Protoser/buttonbox/src/settings.h

// Persistent user settings (NVS flash).
#pragma once
#include <Arduino.h>

static const uint8_t APP_ORDER_MAX = 13;  // launcher-order capacity (>= number of apps in ui.cpp APPS)
static const uint8_t MCDU_MAP_N    = 14;  // physical buttons remappable on the MCDU page (== NUM_HID)
static const uint8_t KEYMAP_N      = 32;  // keyboard binding per output: 0..13 physical, 14..31 chord outputs

// Keyboard modifier bits (settings.keyMod entries) — match the HID left-modifier byte.
static const uint8_t KM_CTRL  = 0x01;
static const uint8_t KM_SHIFT = 0x02;
static const uint8_t KM_ALT   = 0x04;
static const uint8_t KM_GUI   = 0x08;

// Flight-display unit flags (settings.flightUnits bitfield).
static const uint8_t FU_SPEED_MPH = 0x01;  // airspeed in mph (else kt)
static const uint8_t FU_ALT_M     = 0x02;  // altitude in metres (else ft)

// Clock app display flags (settings.clockFlags bitfield).
static const uint8_t CLK_DIGITAL  = 0x01;  // digital readout (else analog dial)
static const uint8_t CLK_SECONDS  = 0x02;  // show the seconds hand / digital seconds
static const uint8_t CLK_NUMERALS = 0x04;  // analog: draw 12/3/6/9 numerals
static const uint8_t CLK_DATE     = 0x08;  // show the weekday/date line
static const uint8_t CLK_24H      = 0x10;  // digital: 24-hour (else 12-hour AM/PM)

struct Settings {
  bool     flipped       = false;  // when true: no screen rotation (panel in non-default position)
  bool     labelsGpio    = false;  // grid labels: false = HID number, true = GPIO
  uint16_t idleBlankSec  = 0;      // blank screen after N s idle (0 = never)
  uint16_t chordWindowMs = 40;     // hold window before a chord member fires solo
  uint8_t  bootSel        = 1;      // power-on screen: 0 = launcher, else app index+1 (see ui.cpp APPS)
  uint8_t  pcStatOrder[5] = {0, 1, 2, 3, 4};  // ordered stat indices 0-7 shown on dash; 0xFF = empty slot
  uint8_t  appOrder[APP_ORDER_MAX] = {0, 1, 2, 3, 4, 5, 6, 7, 8};  // launcher order; values index ui.cpp APPS
  uint16_t appHidden      = 0;               // bitmask: bit i set = app i hidden from launcher (Menu never hidden)
  uint8_t  wifiMode       = 2;               // 0=off, 1=always on, 2=auto (via companion when connected)
  // MCDU page: physical button (HID index) -> MCDU output index (see mcdu.cpp MCDU_OUTPUTS).
  // Default: 5x2 grid -> LSK L1/R1..L5/R5, nav -> scroll + OVFY/CLR.
  uint8_t  mcduMap[MCDU_MAP_N] = {3, 9, 4, 10, 5, 11, 6, 12, 7, 13, 1, 2, 17, 16};
  uint8_t  flightUnits    = 0;               // FU_* bitfield (speed/altitude units on the Flight display)
  uint8_t  engStyle       = 0;               // Engine view: 0 = dial gauges, 1 = bars
  uint16_t timerSec       = 300;             // countdown Timer app: last-used duration (s)
  // Keyboard output: per-output HID key + modifier. Output index (0..13 physical, 14..31 chord).
  // keyKey 0 = unbound (that output emits nothing). Default: the 10 always-on buttons -> F13..F22
  // (phantom keys no real keyboard has, so they never collide); nav + chords start unbound.
  uint8_t  keyKey[KEYMAP_N] = {0x68, 0x69, 0x6A, 0x6B, 0x6C, 0x6D, 0x6E, 0x6F, 0x70, 0x71};
  uint8_t  keyMod[KEYMAP_N] = {0};
  uint8_t  brightFull     = 100;             // active backlight brightness % (5..100)
  uint8_t  brightIdle     = 20;              // dimmed backlight brightness % when idle (0..100)
  uint16_t dimIdleSec     = 15;              // auto-dim to brightIdle after N s idle (0 = never)
  uint8_t  clockFlags     = CLK_NUMERALS | CLK_SECONDS | CLK_DATE | CLK_24H;  // Clock: analog, 12 numerals, seconds+date, 24h
};
extern Settings settings;

void loadSettings();
void saveSettings();

// Mutating helpers (each cycles/toggles the value and persists it).
void settingsToggleFlip();
void settingsToggleLabels();
void settingsCycleIdle();
void settingsCycleChordWin();
void settingsCycleBrightFull();
void settingsCycleBrightIdle();
void settingsCycleDimIdle();
